formatc1702/Pixel-in-my-Closet/Docs/Photos/IMG_2091.JPG

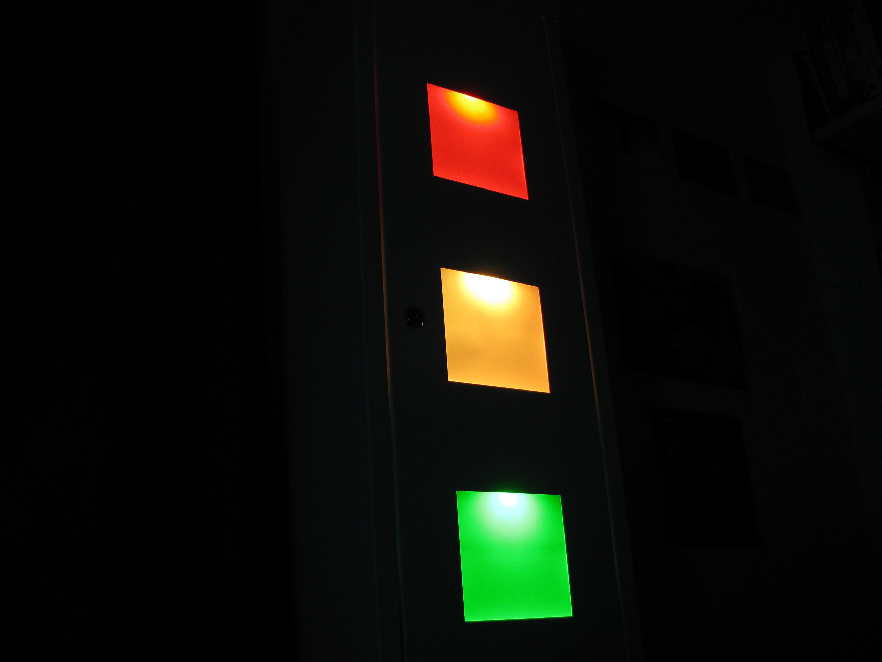
Docs/Photos/IMG_2091.JPG
