formatc1702/Pixel-in-my-Closet/Docs/Photos/IMG_2064.JPG

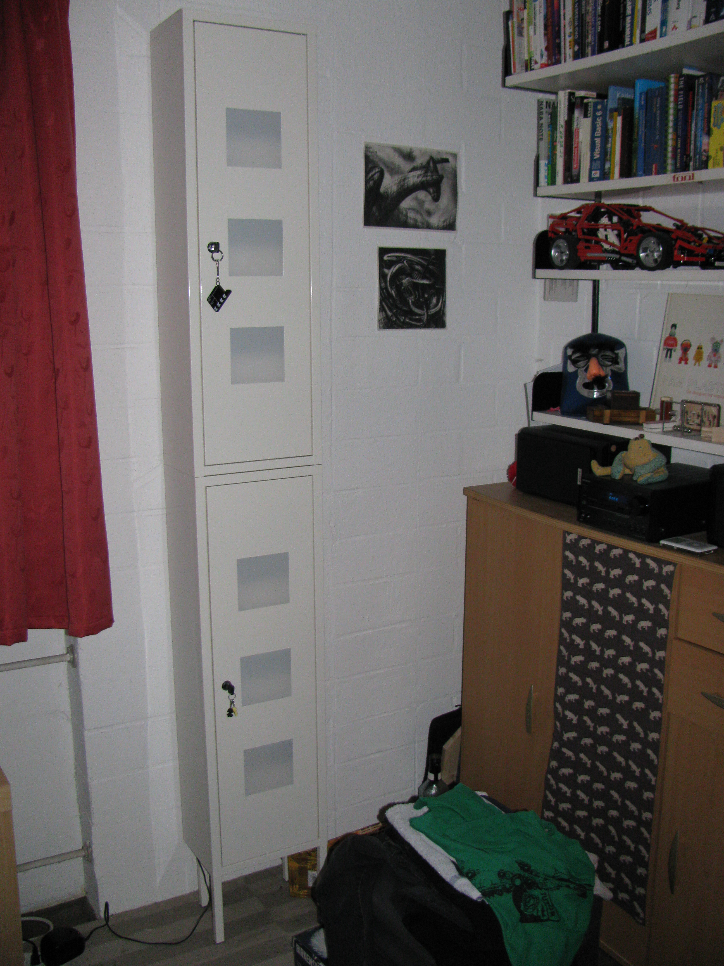
Docs/Photos/IMG_2064.JPG
